grontis/ed2-handForceController/ed2-UnityProject/Assets/FPS_demo/Asset Packs/Standard Assets/CrossPlatformInput/Sprites/ButtonCameraCycleUpSprite.png

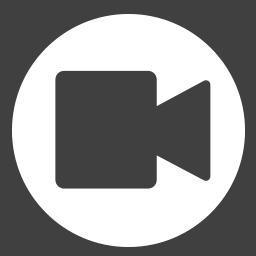
ed2-UnityProject/Assets/FPS_demo/Asset Packs/Standard Assets/CrossPlatformInput/Sprites/ButtonCameraCycleUpSprite.png
