grontis/ed2-handForceController/ed2-UnityProject/Assets/FPS_demo/Asset Packs/Standard Assets/Effects/GlassRefraction/Textures/GlassStainedNormals.tif

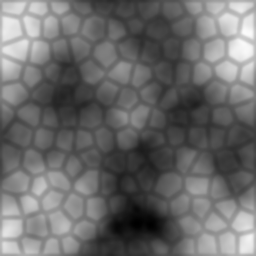
ed2-UnityProject/Assets/FPS_demo/Asset Packs/Standard Assets/Effects/GlassRefraction/Textures/GlassStainedNormals.tif
