grontis/ed2-handForceController/ed2-UnityProject/Assets/FPS_demo/Asset Packs/Standard Assets/Effects/LightCookies/Textures/FlashlightIrregularCookie.tif

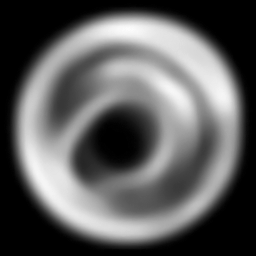
ed2-UnityProject/Assets/FPS_demo/Asset Packs/Standard Assets/Effects/LightCookies/Textures/FlashlightIrregularCookie.tif
