grontis/ed2-handForceController/ed2-UnityProject/Assets/FPS_demo/Asset Packs/Standard Assets/Effects/TessellationShaders/Textures/CliffNormals.png

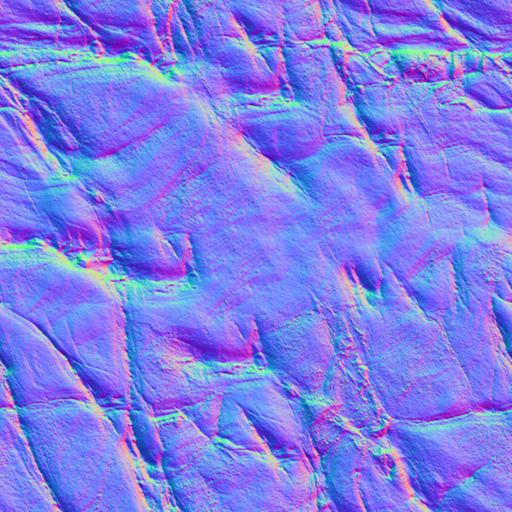
ed2-UnityProject/Assets/FPS_demo/Asset Packs/Standard Assets/Effects/TessellationShaders/Textures/CliffNormals.png
