grontis/ed2-handForceController/ed2-UnityProject/Assets/FPS_demo/Asset Packs/Standard Assets/Environment/SpeedTree/Palm/Thumb_Palm_Desktop.jpg

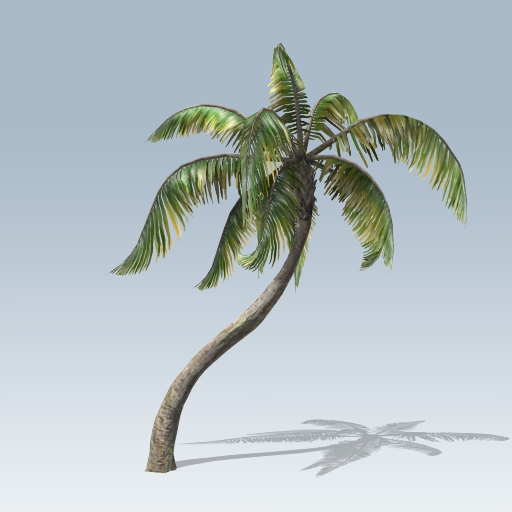
ed2-UnityProject/Assets/FPS_demo/Asset Packs/Standard Assets/Environment/SpeedTree/Palm/Thumb_Palm_Desktop.jpg
