grontis/ed2-handForceController/ed2-UnityProject/Assets/FPS_demo/Asset Packs/Standard Assets/Environment/TerrainAssets/SurfaceTextures/MudRockyNormals.bmp

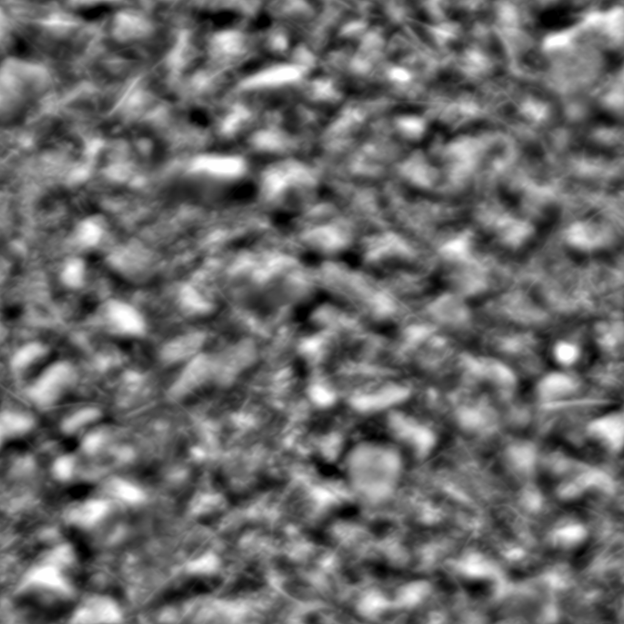
ed2-UnityProject/Assets/FPS_demo/Asset Packs/Standard Assets/Environment/TerrainAssets/SurfaceTextures/MudRockyNormals.bmp
