grontis/ed2-handForceController/ed2-UnityProject/Assets/FPS_demo/Asset Packs/Standard Assets/Environment/Water (Basic)/Textures/WaterBasicNormals.jpg

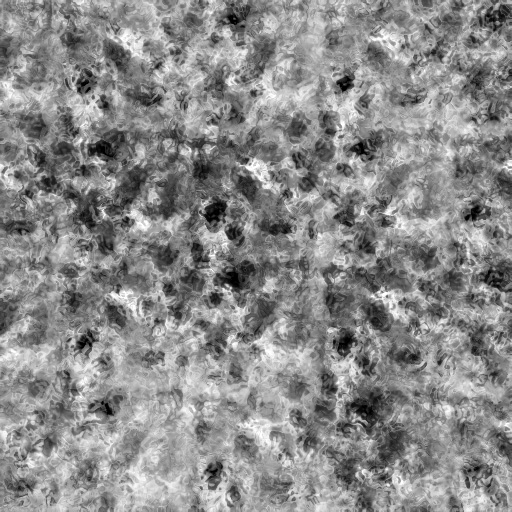
ed2-UnityProject/Assets/FPS_demo/Asset Packs/Standard Assets/Environment/Water (Basic)/Textures/WaterBasicNormals.jpg
