grontis/ed2-handForceController/ed2-UnityProject/Assets/FPS_demo/Asset Packs/Standard Assets/Environment/Water/Water4/Textures/SimpleFoam.png

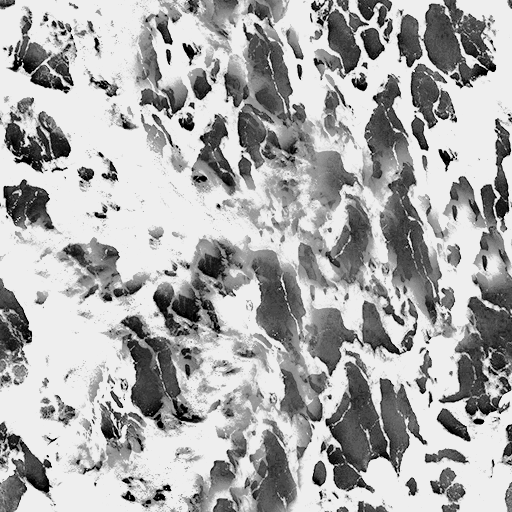
ed2-UnityProject/Assets/FPS_demo/Asset Packs/Standard Assets/Environment/Water/Water4/Textures/SimpleFoam.png
