grontis/ed2-handForceController/ed2-UnityProject/Assets/FPS_demo/Asset Packs/Standard Assets/ParticleSystems/Textures/ParticleCloudBlack.png

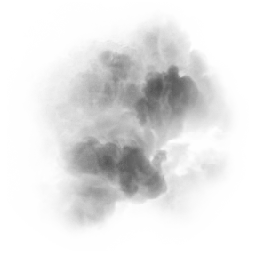
ed2-UnityProject/Assets/FPS_demo/Asset Packs/Standard Assets/ParticleSystems/Textures/ParticleCloudBlack.png
