grontis/ed2-handForceController/ed2-UnityProject/Assets/FPS_demo/Images/GUIReticle.png

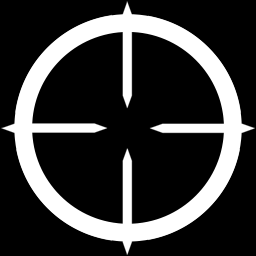
ed2-UnityProject/Assets/FPS_demo/Images/GUIReticle.png
