grontis/ed2-handForceController/ed2-UnityProject/Assets/FPS_demo/Images/Splatter.png

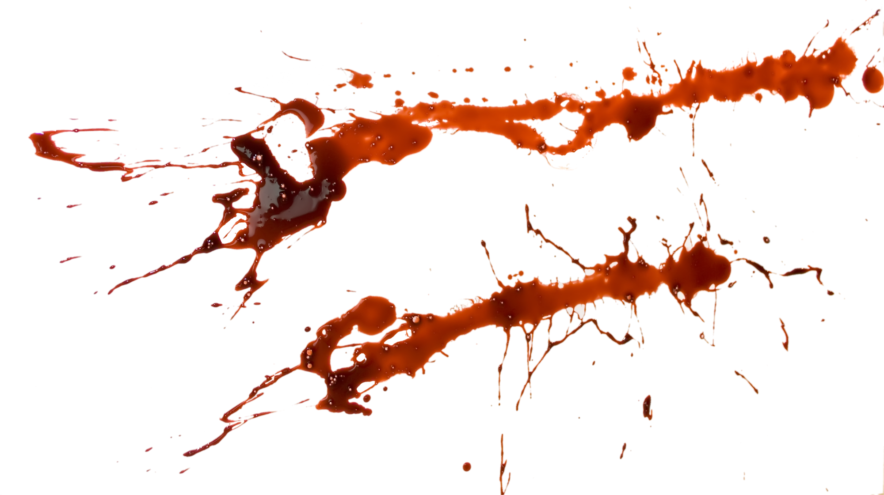
ed2-UnityProject/Assets/FPS_demo/Images/Splatter.png
