grontis/ed2-handForceController/ed2-UnityProject/Assets/FPS_demo/Images/ZR-Level-Plan.jpg

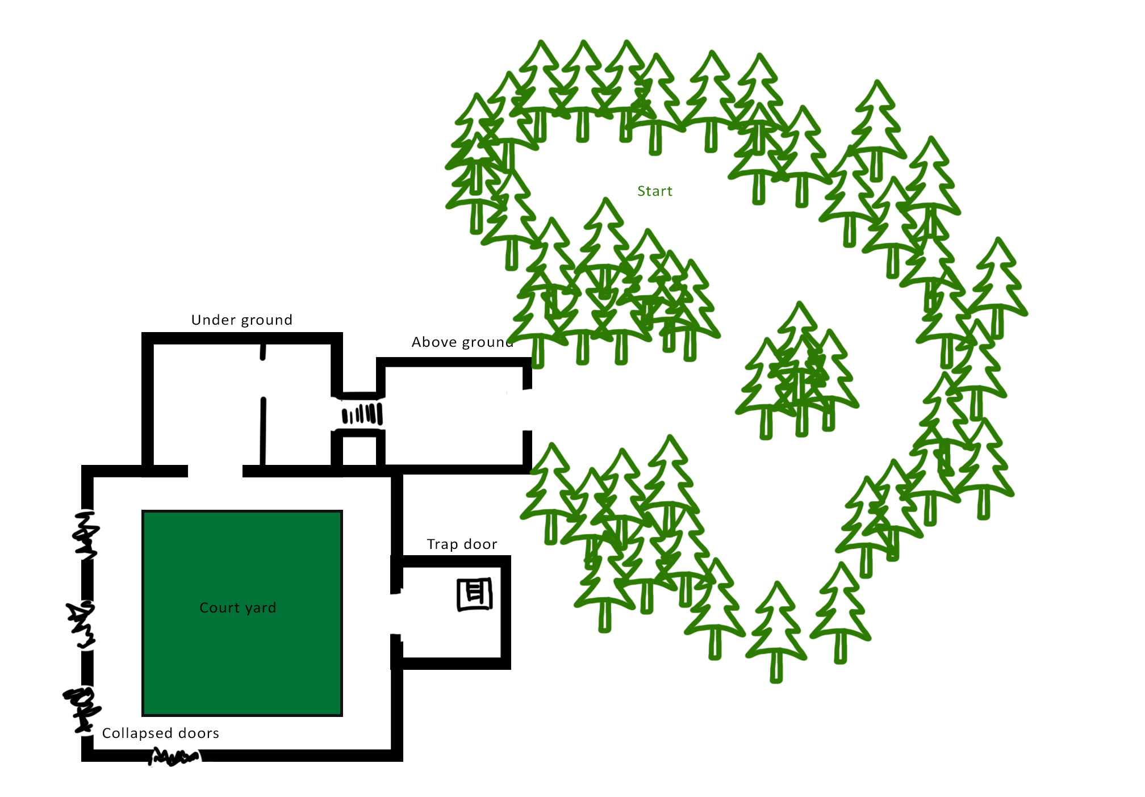
ed2-UnityProject/Assets/FPS_demo/Images/ZR-Level-Plan.jpg
