grontis/ed2-handForceController/ed2-UnityProject/Assets/FPS_demo/Prefabs/Sci Fi Gun Light/_textures/GunTwo/Black/GunTwo_SpecularSmoothness.png

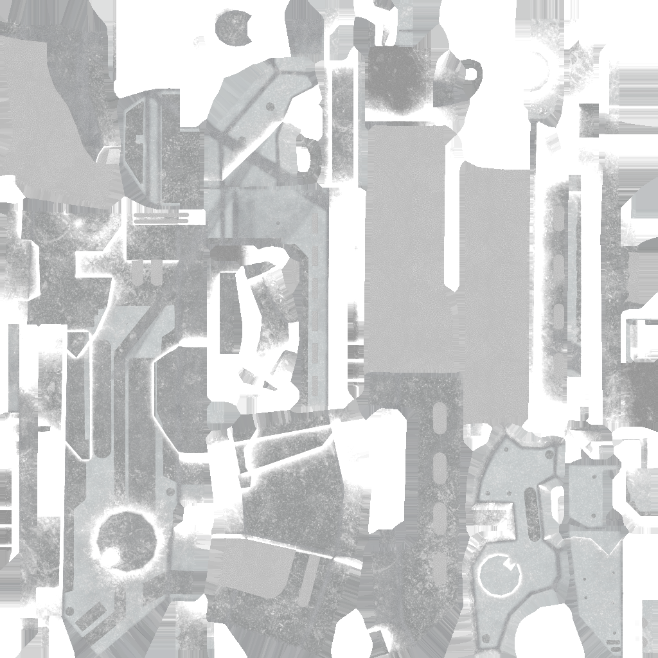
ed2-UnityProject/Assets/FPS_demo/Prefabs/Sci Fi Gun Light/_textures/GunTwo/Black/GunTwo_SpecularSmoothness.png
