grontis/ed2-handForceController/ed2-UnityProject/Assets/FPS_demo/Prefabs/Sci Fi Gun Light/_textures/GunTwo/GunTwo_Emission1.png

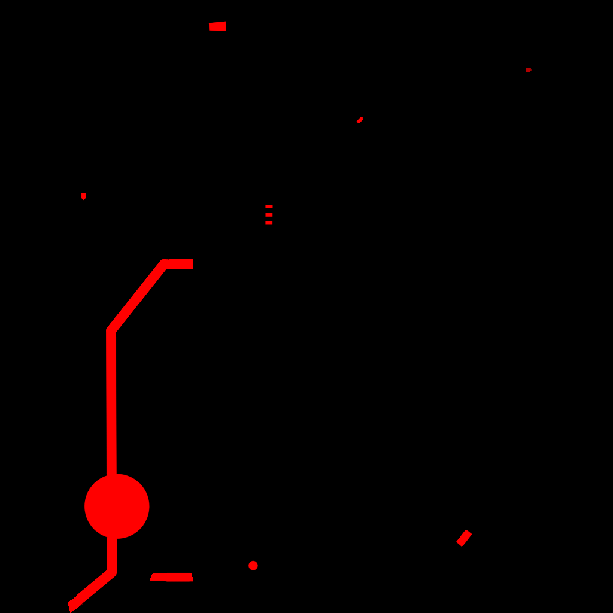
ed2-UnityProject/Assets/FPS_demo/Prefabs/Sci Fi Gun Light/_textures/GunTwo/GunTwo_Emission1.png
