grontis/ed2-handForceController/ed2-UnityProject/Assets/FPS_demo/Prefabs/TextMesh Pro/Sprites/EmojiOne.png

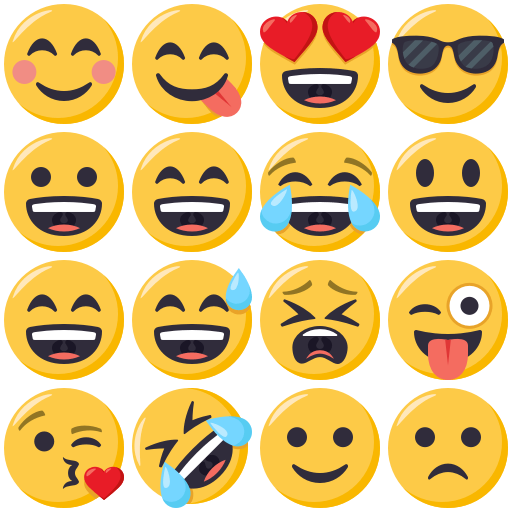
ed2-UnityProject/Assets/FPS_demo/Prefabs/TextMesh Pro/Sprites/EmojiOne.png
