grontis/ed2-handForceController/ed2-UnityProject/Assets/FPS_demo/Prefabs/Zombie/Textures/Zombie_ao.png

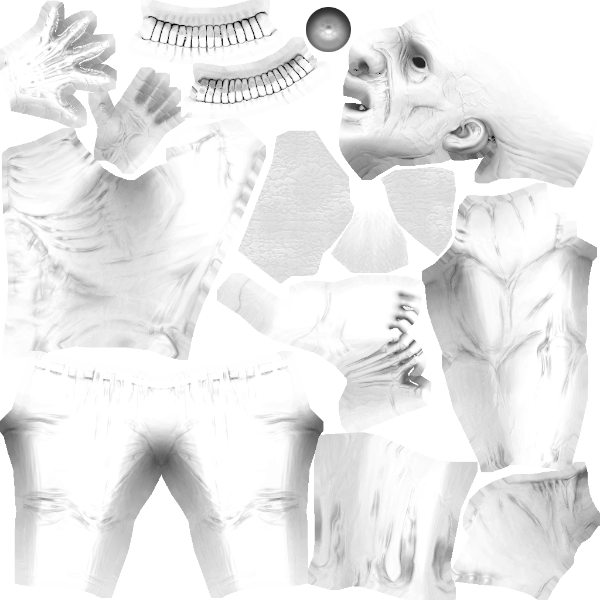
ed2-UnityProject/Assets/FPS_demo/Prefabs/Zombie/Textures/Zombie_ao.png
