grontis/ed2-handForceController/ed2-UnityProject/Assets/FPS_demo/Prefabs/Zombie/Textures/Zombie_nm.png

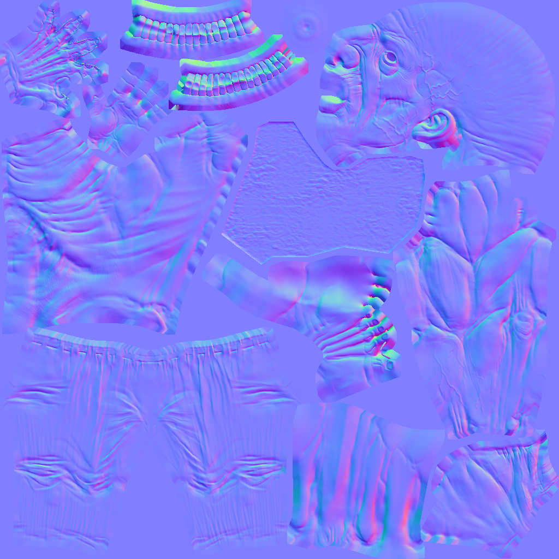
ed2-UnityProject/Assets/FPS_demo/Prefabs/Zombie/Textures/Zombie_nm.png
