grontis/ed2-handForceController/ed2-UnityProject/Assets/Scenes/FPSLevel1/Lightmap-1_comp_dir.png

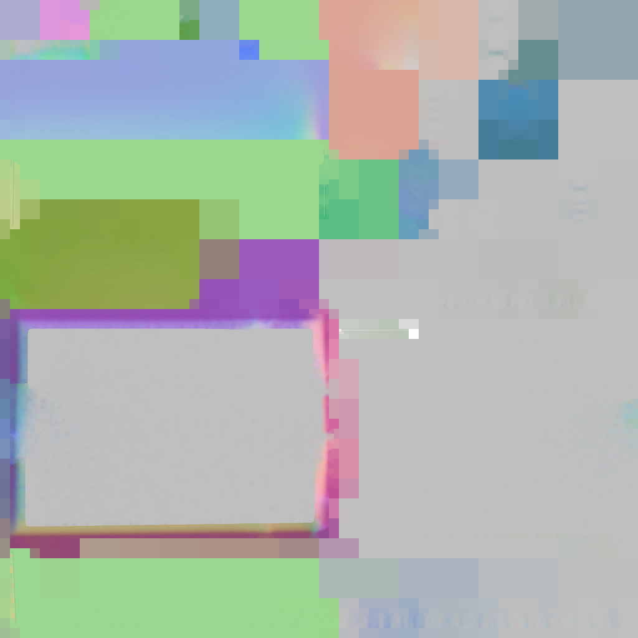
ed2-UnityProject/Assets/Scenes/FPSLevel1/Lightmap-1_comp_dir.png
