grontis/ed2-handForceController/ed2-UnityProject/Assets/Scenes/FPSLevel1/Lightmap-2_comp_dir.png

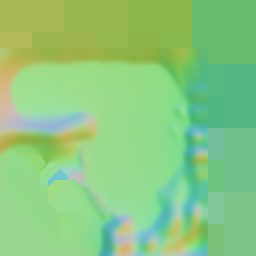
ed2-UnityProject/Assets/Scenes/FPSLevel1/Lightmap-2_comp_dir.png
